Protocentral/protocentral_ads1293/docs/img/IMG_20201109_210016288.jpg

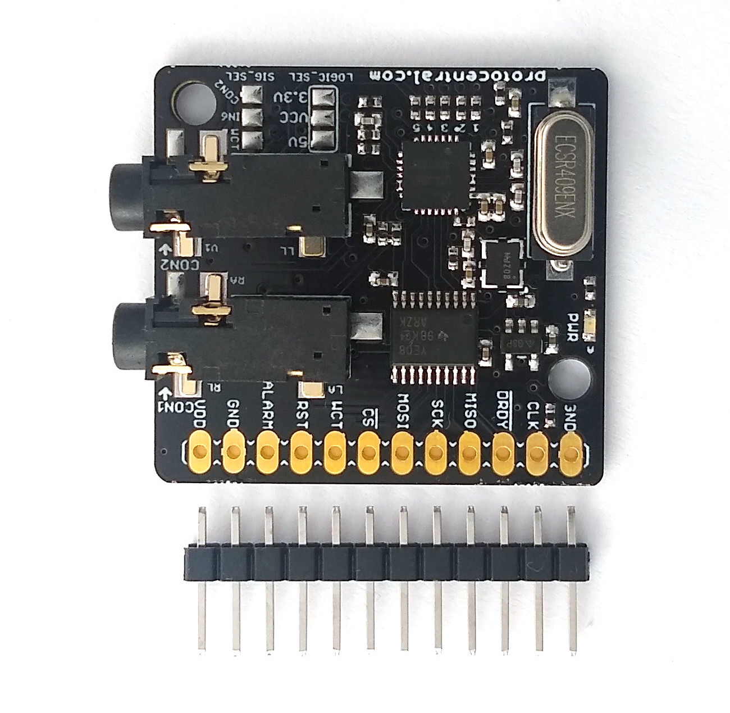
docs/img/IMG_20201109_210016288.jpg
